WKHarmon/led-sectional/firmware/extra_script.py

# PlatformIO Extra Script
# This script runs before the build process
#
# Currently a placeholder for future build customization
# Examples of what could be added:
# - Auto-versioning from git tags
# - Build timestamp injection
# - Environment-specific configuration

Import("env")

# Example: Print build info
# print("Building LED Sectional firmware...")

# Example: Add custom build flags based on environment
# env.Append(CPPDEFINES=[("BUILD_TIME", env.get("BUILD_TIME", "unknown"))])
